andrebroekman/ultrasonic-parking-distance-sensor/KiCad/Lidar sensor.kicad_sch

## KiCad design KiCad/Lidar sensor.kicad_sch (2024-12-01)

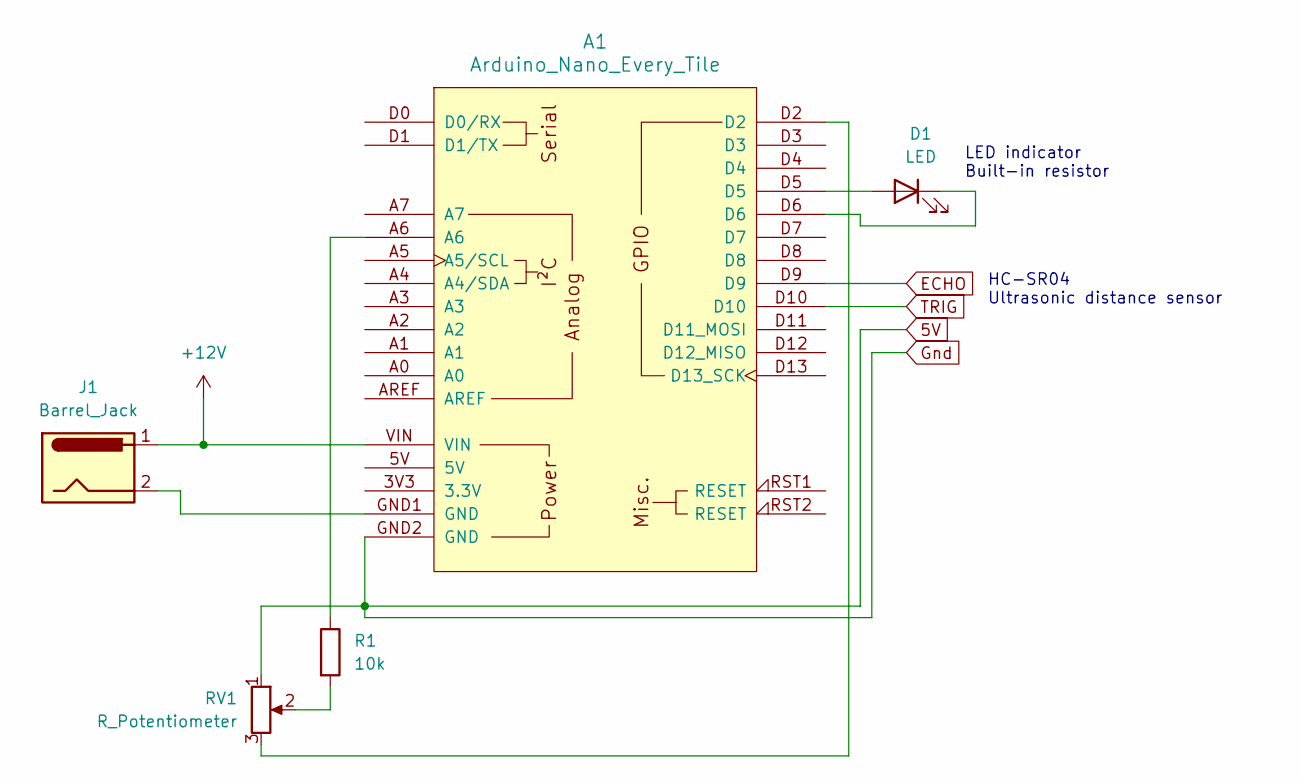
[picture p4: schematic Lidar sensor.kicad_sch]

Parts:
A1: Arduino_Nano_Every_Tile
D1: LED
J1: Barrel_Jack
R1: 10k
RV1: R_Potentiometer

Connections:
5V: A1.GND2 (GND), RV1.1
+12V: A1.VIN, J1.1
ECHO: A1.D9
unnamed: A1.A6, R1.1
unnamed: A1.D2, RV1.3
unnamed: A1.D5, D1.2 (A)
unnamed: A1.D6, D1.1 (K)
unnamed: A1.GND1 (GND), J1.2
unnamed: R1.2, RV1.2
TRIG: A1.D10

Notes on the sheet:
LED indicator Built-in resistor
HC-SR04 Ultrasonic distance sensor
